PaulKlinger/cnn_card/cnn_card_embedded_code.X/fun/startup_anim.c

#include "../util/led_control.h"
#include "../config.h"

#include <avr/io.h>
#include <util/delay.h>
#include <avr/interrupt.h>


void run_startup_animation() {
    clear_led_brightness();
    update_pwm_pattern();
    run_pwm_cycle();
    

    const uint8_t brightness_sequence[] = {
        0,0,0,0,0,0,0,0,0,0,0,0,0,0,0,0,
        value_to_pwm_level(5., 5),
        value_to_pwm_level(4., 5),
        value_to_pwm_level(3., 5),
        value_to_pwm_level(2., 5),
        value_to_pwm_level(1., 5),
    };
    
    uint8_t pwm_val;
    for (uint8_t i=0; i<sizeof(brightness_sequence); i++) {
        /* autogenerated code from led_animation_layout.ipynb */
        pwm_val = brightness_sequence[(i + 15) % sizeof(brightness_sequence)];
        set_led_brightness(8, 3, pwm_val);
        run_pwm_cycle();
        pwm_val = brightness_sequence[(i + 14) % sizeof(brightness_sequence)];
        set_led_brightness(8, 4, pwm_val);
        pwm_val = brightness_sequence[(i + 13) % sizeof(brightness_sequence)];
        set_led_brightness(2, 6, pwm_val);
        set_led_brightness(8, 5, pwm_val);
        set_led_brightness(8, 6, pwm_val);
        pwm_val = brightness_sequence[(i + 12) % sizeof(brightness_sequence)];
        set_led_brightness(3, 5, pwm_val);
        set_led_brightness(1, 7, pwm_val);
        set_led_brightness(5, 0, pwm_val);
        set_led_brightness(8, 7, pwm_val);
        set_led_brightness(8, 8, pwm_val);
        set_led_brightness(8, 1, pwm_val);
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
        pwm_val = brightness_sequence[(i + 1) % sizeof(brightness_sequence)];
        set_led_brightness(1, 0, pwm_val);
        pwm_val = brightness_sequence[(i + 0) % sizeof(brightness_sequence)];
        set_led_brightness(0, 0, pwm_val);

        update_pwm_pattern();
    }
}
