PaulKlinger/cnn_card/cnn_card_embedded_code.X/model/model_weights.c

#include "tensor.h"

/* 99th percentile of activations per layer
 * copied from cnn/train.ipynb
 */

const float conv0_activation_99per = 3.298433542251587;
const float conv1_activation_99per = 4.464225769042969;
const float conv2_activation_99per = 5.400259494781494;

/* weight tensor data (definitions below)
 * (copied from cnn/train.ipynb)
 */

const float conv0_kernel_data[] = {
    7.020391e-01, 1.0258303e+00, 8.72381e-01, -1.1648293e+00, 9.5234656e-01,
    7.509327e-01, -9.5353985e-01, -8.4196067e-01, 1.0978298e+00, 1.032137e+00,
    8.4567595e-01, 6.5854657e-01, -5.5697376e-01, 1.4566342e+00, -4.1969696e-01,
    9.727429e-01,
};

const float conv0_bias_data[] = {
    -1.446728e-01, -2.1616767e-01, 5.0059897e-01, 5.065947e-01,
};

const float conv1_kernel_data[] = {
    4.2334983e-01, 1.274771e-01, -1.3428767e-01, 7.536915e-01, -3.5425636e-01,
    9.6646294e-02, 1.6611163e-01, 5.1564974e-01, -9.327773e-02, -1.809538e-01,
    3.956333e-01, 5.099228e-01, 3.4310982e-01, 3.0296388e-01, -1.6110633e-01,
    4.999903e-01, 4.2740902e-01, -1.3602641e-01, 1.5409742e-01, 1.3710105e-01,
    2.734646e-01, -6.895231e-01, 5.1433768e-02, 1.4937659e-01, -9.385792e-02,
    2.3060943e-01, -7.2521734e-01, -2.5629053e-01, -1.8719584e-01, 2.724104e-01,
    1.24459326e-01, 5.3574786e-02, -1.273949e-01, 2.6588535e-01, -4.7672948e-01,
    -5.9506856e-02, 2.1918508e-01, 3.8890484e-01, -5.388753e-01, 2.488933e-01,
    -3.747219e-01, 3.6291236e-01, 1.9091092e-01, -2.7426612e-01, -6.6629425e-02,
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
    -6.3095856e-01, 8.462711e-01, 1.0806475e-02, -2.2370462e+00, 4.7786728e-01,
    1.2399755e+00, -2.9211602e+00, -1.7445532e+00, 4.9983785e-02, -7.516006e-01,
    -1.1201372e+00, -1.7433944e+00, 1.6023718e+00, -2.6503468e+00, -1.2129475e+00,
    2.0043445e+00, -1.3965753e+00, 9.559851e-02, 5.4492116e-01, 1.4797763e-02,
    -7.8738564e-01, 2.326161e+00, 1.1061105e+00, -7.3313093e-01, 1.975456e+00,
};

const float dense_bias_data[] = {
    1.8121316e+00, -5.4363614e-01, -1.3337061e+00, 2.1079712e-01, 8.1284297e-01,
    3.3748004e-01, -6.7212075e-01, 3.100645e-01, 3.179907e-01, -9.563908e-01,
};


/* Weight tensor definitions */

const struct float_4tensor conv0_kernel = {
    .data=(float*) conv0_kernel_data,
    .s0=2, // rows
    .s1=2, // cols
    .s2=1, // input channels
    .s3=4  // filters
};


const struct float_4tensor conv0_bias = {
    .data=(float*) conv0_bias_data,
    .s0=4, // channels
    .s1=1,
    .s2=1,
    .s3=1 
};

const struct float_4tensor conv1_kernel = {
    .data=(float*) conv1_kernel_data,
    .s0=2, // rows
    .s1=2, // cols
    .s2=4, // input channels
    .s3=8  // filters
};

const struct float_4tensor conv1_bias = {
    .data=(float*) conv1_bias_data,
    .s0=8, // channels
    .s1=1,
    .s2=1,
    .s3=1 
};

const struct float_4tensor conv2_kernel = {
    .data=(float*) conv2_kernel_data,
    .s0=2, // rows
    .s1=2, // cols
    .s2=8, // input channels
    .s3=16  // filters
};

const struct float_4tensor conv2_bias = {
    .data=(float*) conv2_bias_data,
    .s0=16, // channels
    .s1=1,
    .s2=1,
    .s3=1 
};

const struct float_4tensor dense_kernel = {
    .data=(float*) dense_kernel_data,
    .s0=10, // units
    .s1=16, // input channels
    .s2=1,
    .s3=1
};

const struct float_4tensor dense_bias = {
    .data=(float*) dense_bias_data,
    .s0=10, // units
    .s1=1,
    .s2=1,
    .s3=1 
};
