PaulKlinger/cnn_card/cnn_card_embedded_code.X/model/model.h

/* 
 * File:   model.h
 * Author: kling
 *
 * Created on 27 September 2020, 17:37
 */

#ifndef MODEL_H
#define	MODEL_H

#include <stdint.h>

#ifdef	__cplusplus
extern "C" {
#endif

    void run_model_and_set_led_brightness(uint8_t filter_idx);


#ifdef	__cplusplus
}
#endif

#endif	/* MODEL_H */
