PaulKlinger/cnn_card/cnn_card_embedded_code.X/fun/startup_anim.h

/* 
 * File:   startup_anim.h
 * Author: kling
 *
 * Created on 03 October 2020, 23:53
 */

#ifndef STARTUP_ANIM_H
#define	STARTUP_ANIM_H

#ifdef	__cplusplus
extern "C" {
#endif

    void run_startup_animation();


#ifdef	__cplusplus
}
#endif

#endif	/* STARTUP_ANIM_H */
