PaulKlinger/cnn_card/cnn_card_embedded_code.X/util/sleep.h

/* 
 * File:   sleep.h
 * Author: kling
 *
 * Created on 08 November 2020, 21:31
 */

#ifndef SLEEP_H
#define	SLEEP_H

#ifdef	__cplusplus
extern "C" {
#endif

    void go_to_sleep();
    void reset_rtc_cnt();


#ifdef	__cplusplus
}
#endif

#endif	/* SLEEP_H */
